louismessonnier/gd-keypad/images/differential-pair-calculation.png

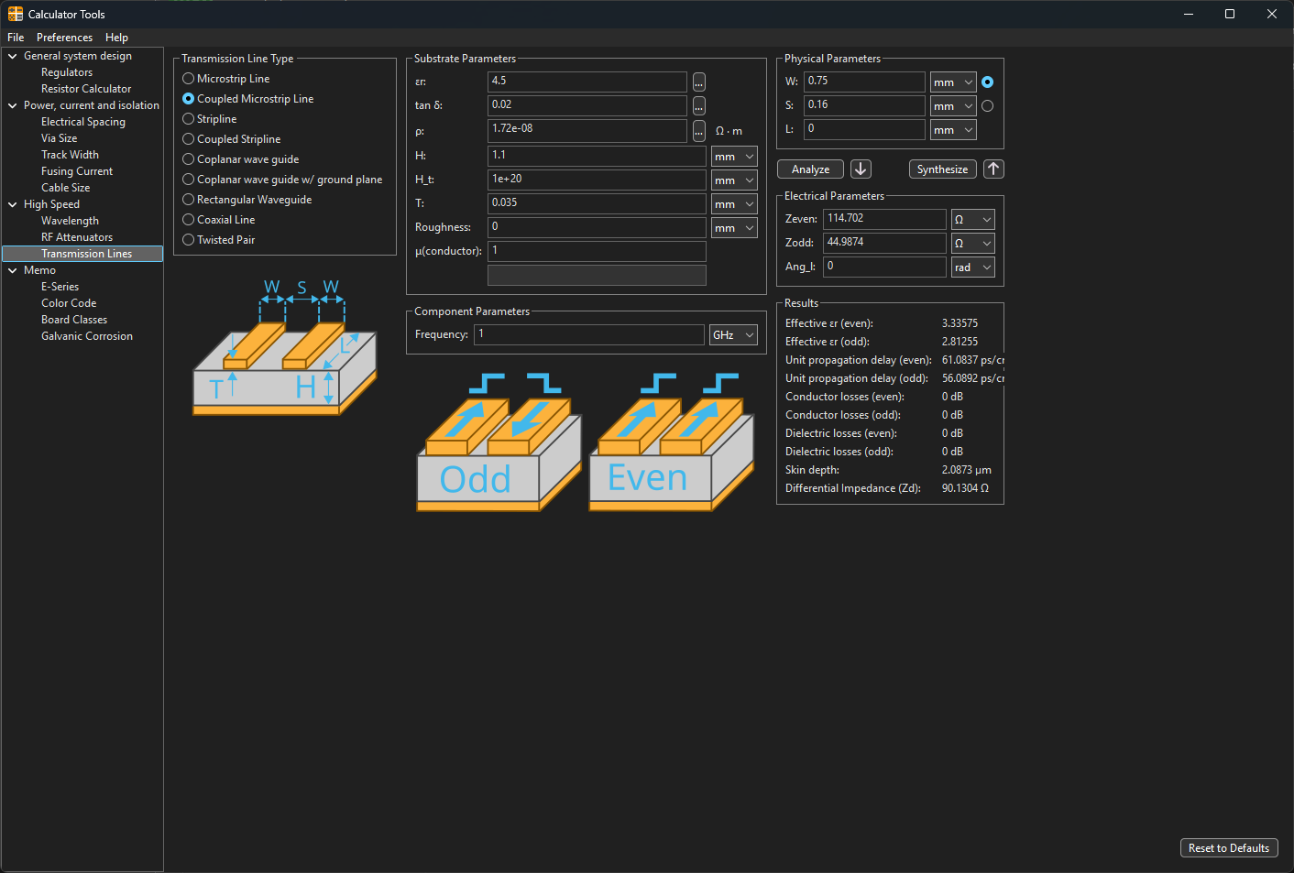
images/differential-pair-calculation.png
