louismessonnier/gd-keypad/images/gd-keypad_pcb_layout_front.png

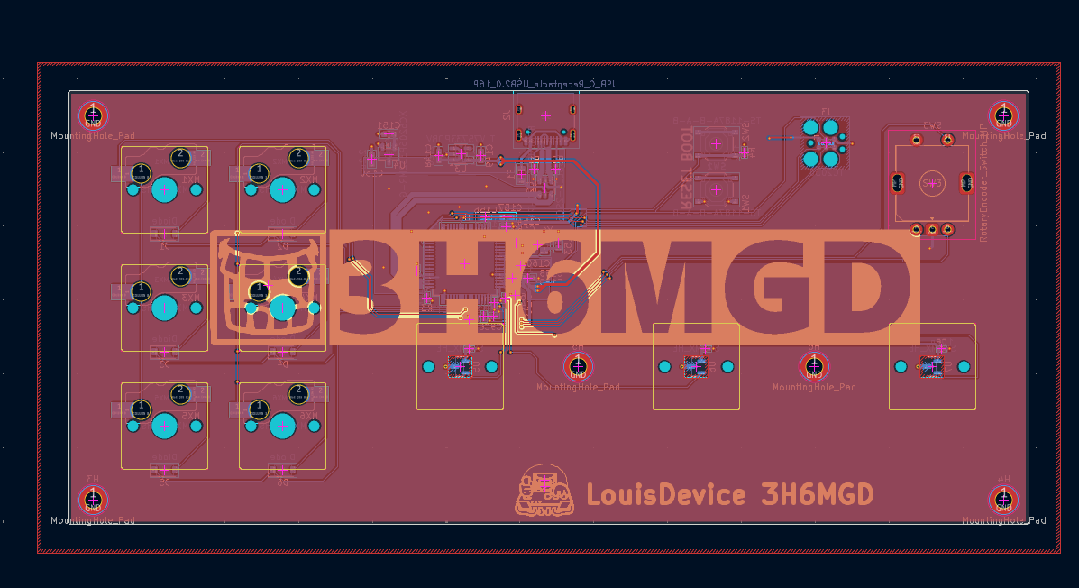
images/gd-keypad_pcb_layout_front.png
