louismessonnier/gd-keypad/images/keyboard-switch_dimensions.webp

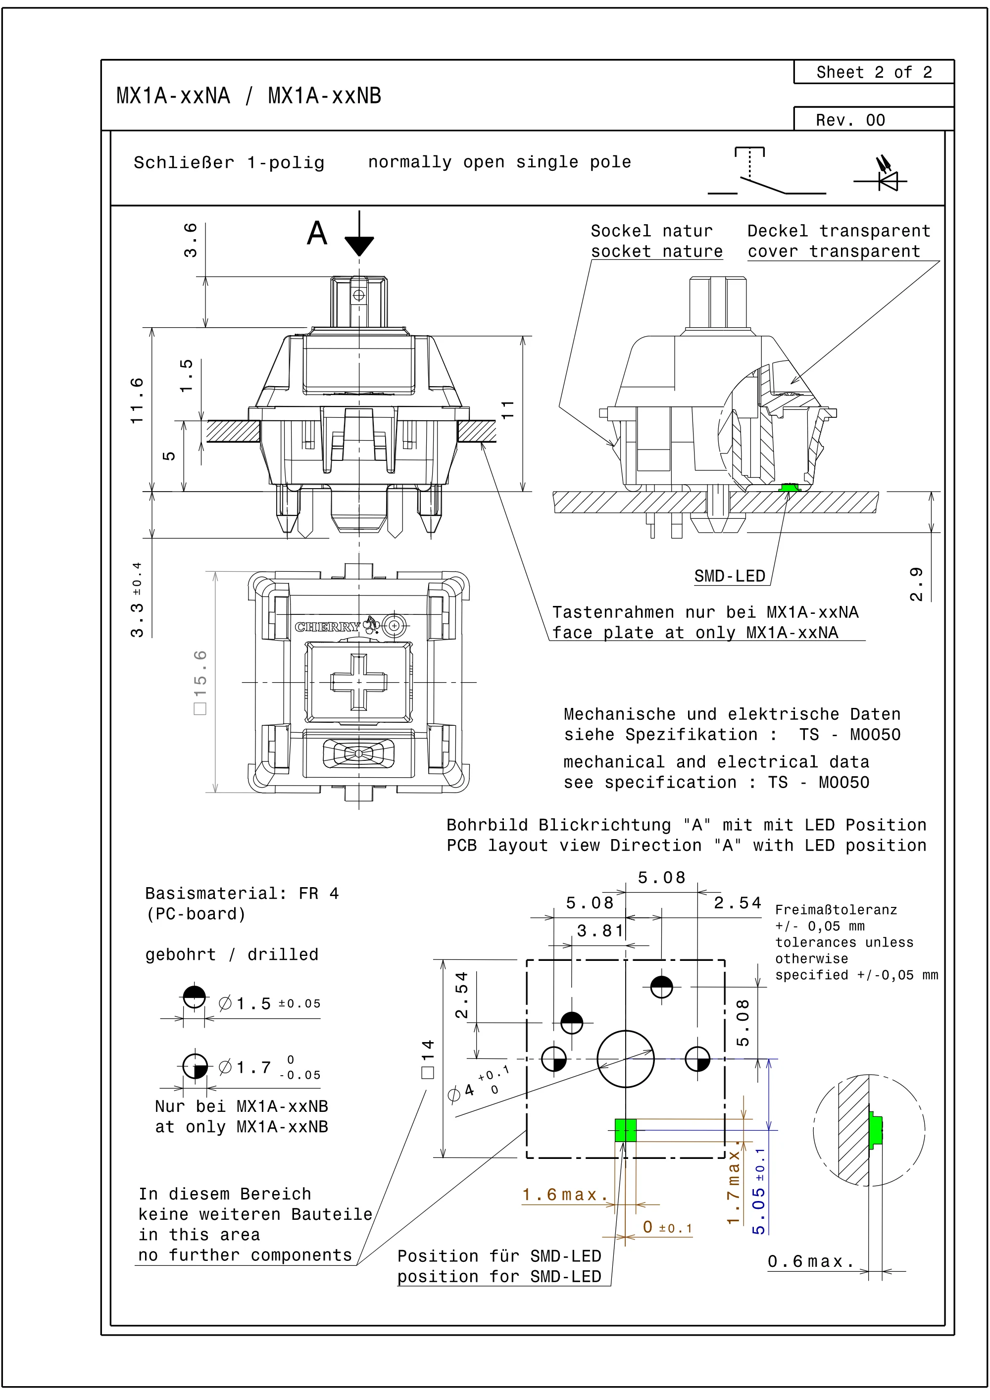
images/keyboard-switch_dimensions.webp
