louismessonnier/gd-keypad/images/gd-keypad_assembly_front.PNG

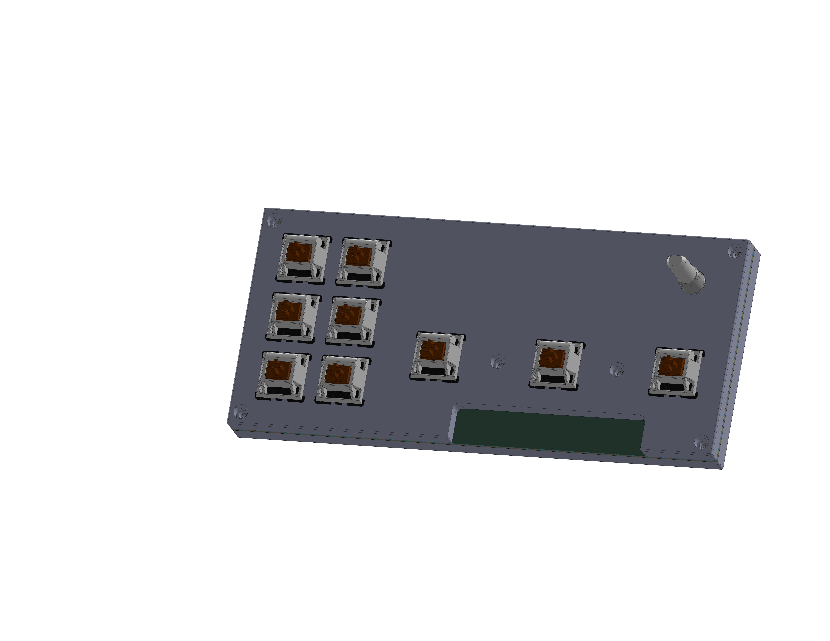
images/gd-keypad_assembly_front.PNG
